Noctisera/E-Book_Reader/Images/Battery v1.png

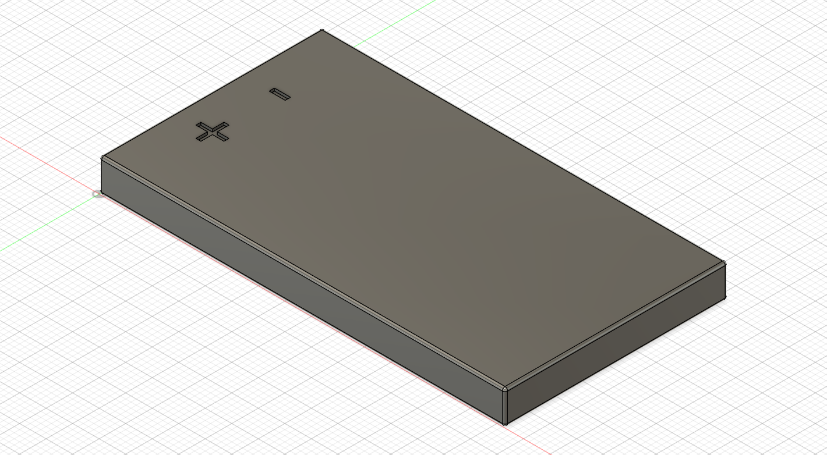
Images/Battery v1.png
